antonjan/africube_receiver_board/gerber/msisdr-F_SilkS.pdf

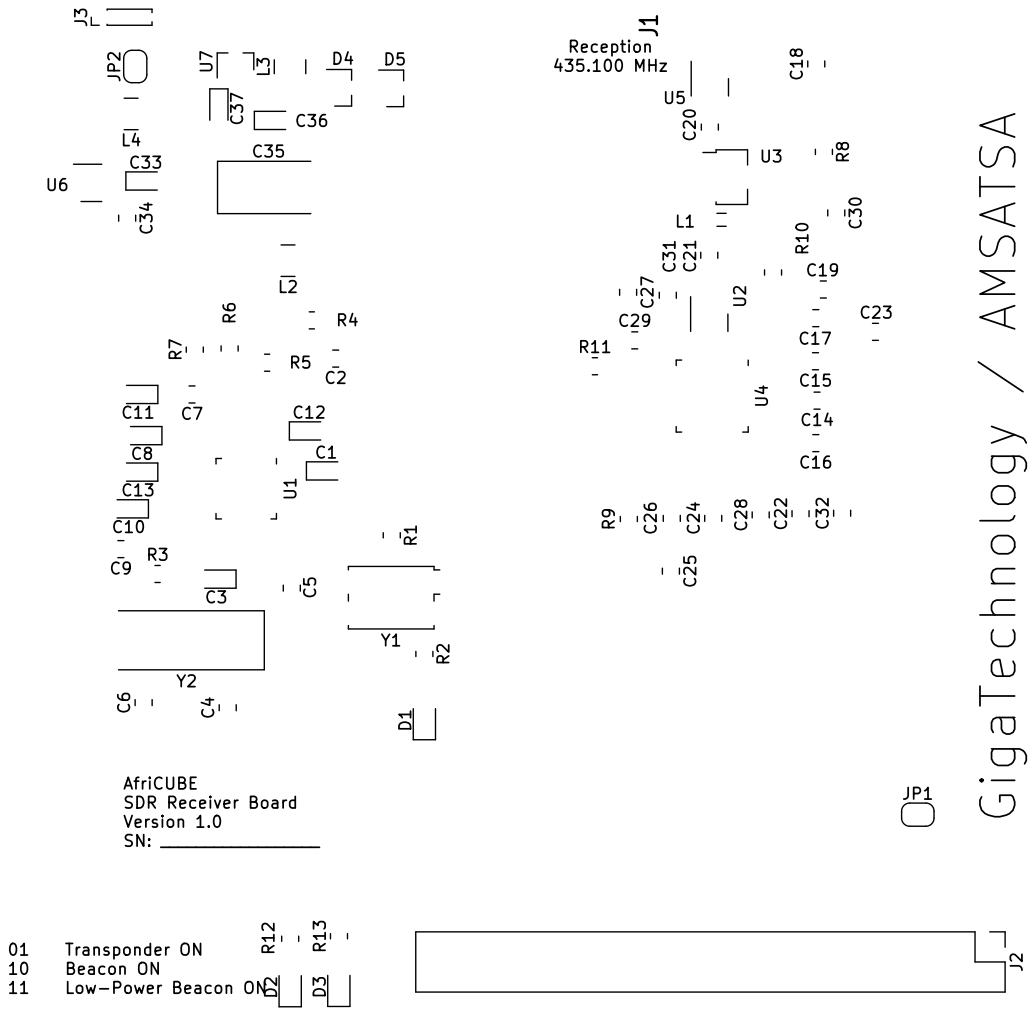
[picture p13: page 1]

01 Transponder ON
10 Beacon ON
11 Low-Power Beacon ON
