antonjan/africube_receiver_board/msiSDR-master/gerber/msisdr-F_SilkS.pdf

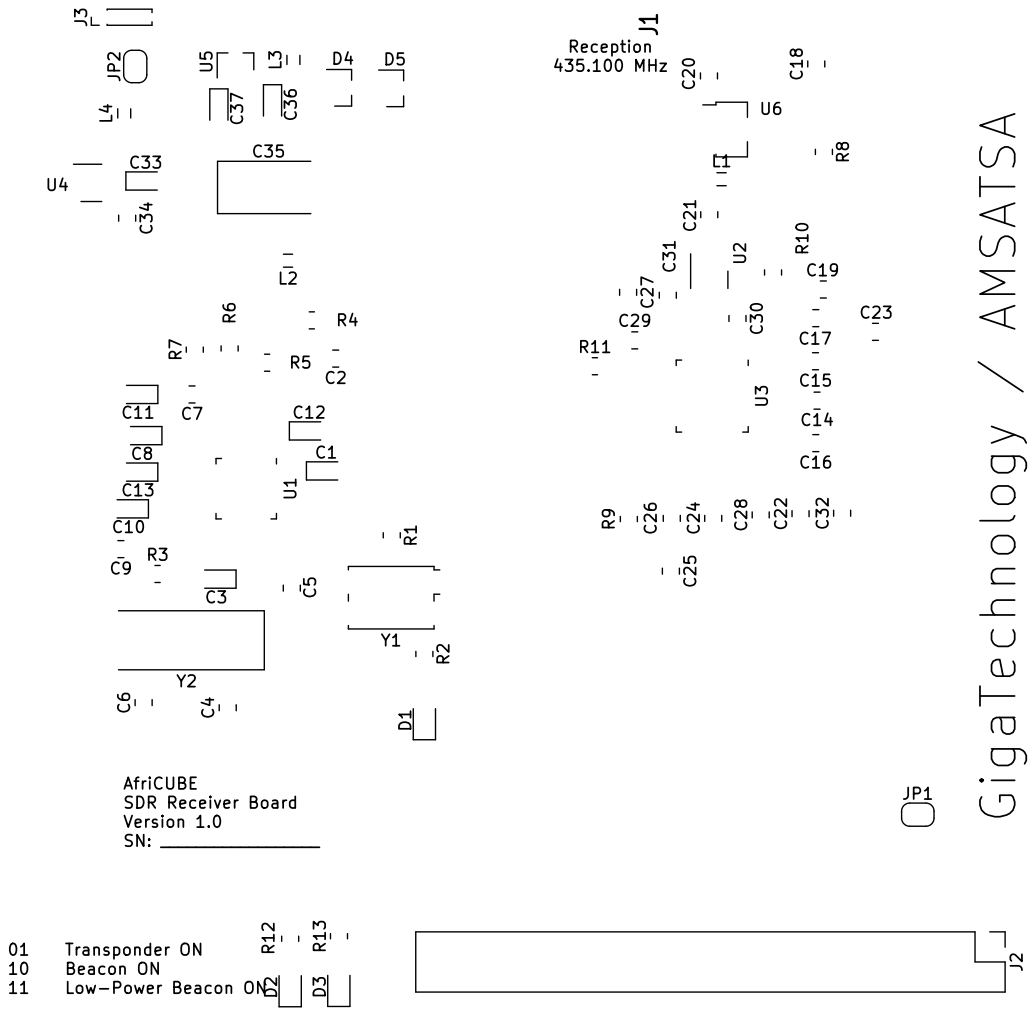
[picture p14: page 1]

01 Transponder ON
10 Beacon ON
11 Low-Power Beacon ON
