antonjan/africube_receiver_board/gerber/msisdr-Edge_Cuts.pdf

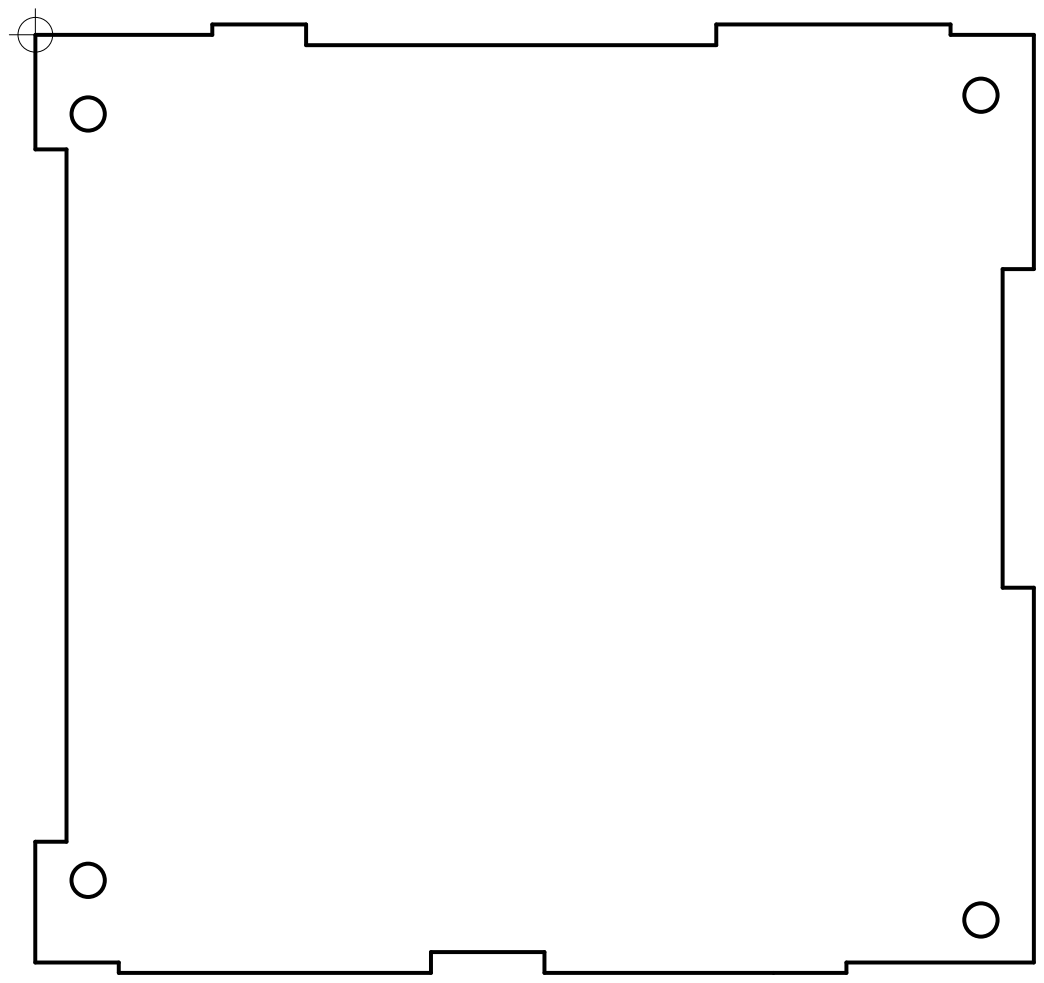
[picture p20: page 1]
