antonjan/africube_receiver_board/gerber/msisdr-F_Cu.pdf

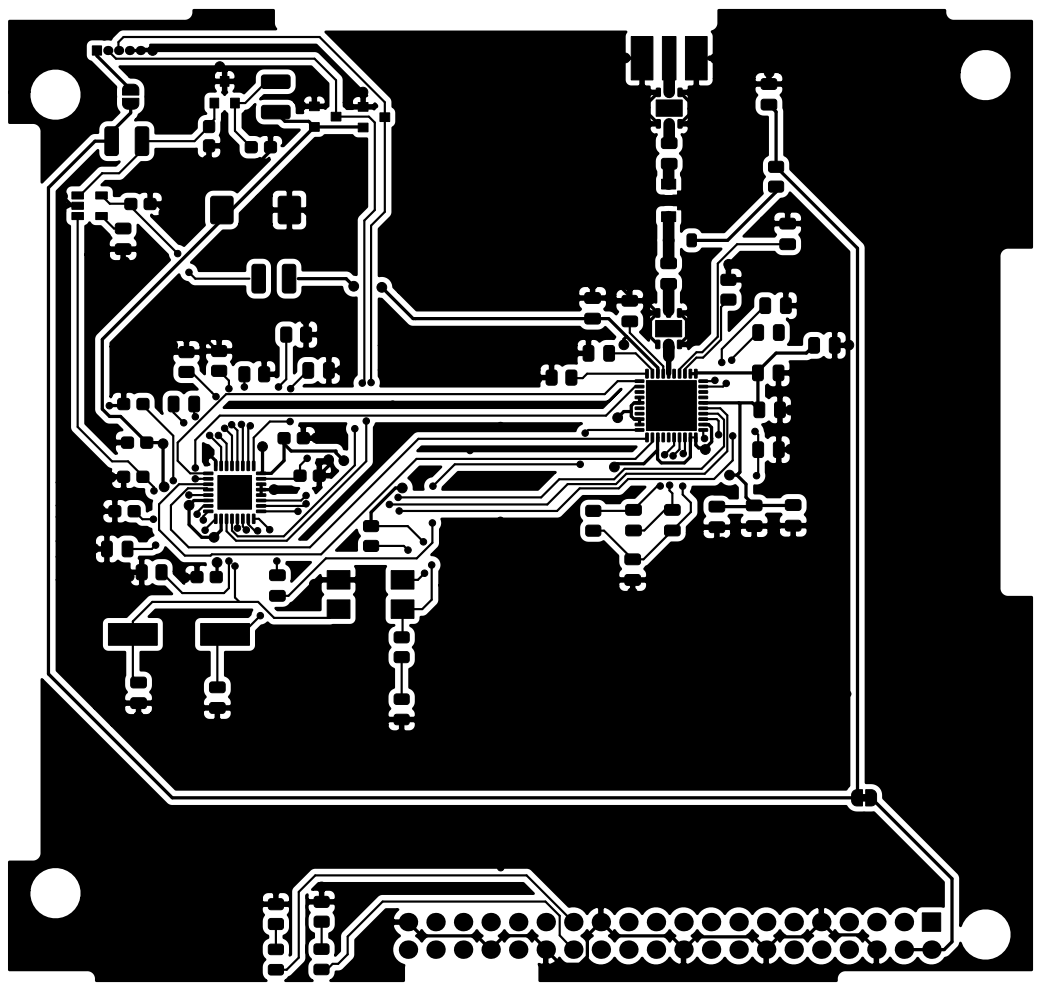
[picture p21: page 1]
