antonjan/africube_receiver_board/gerber/msisdr-F_Mask.pdf

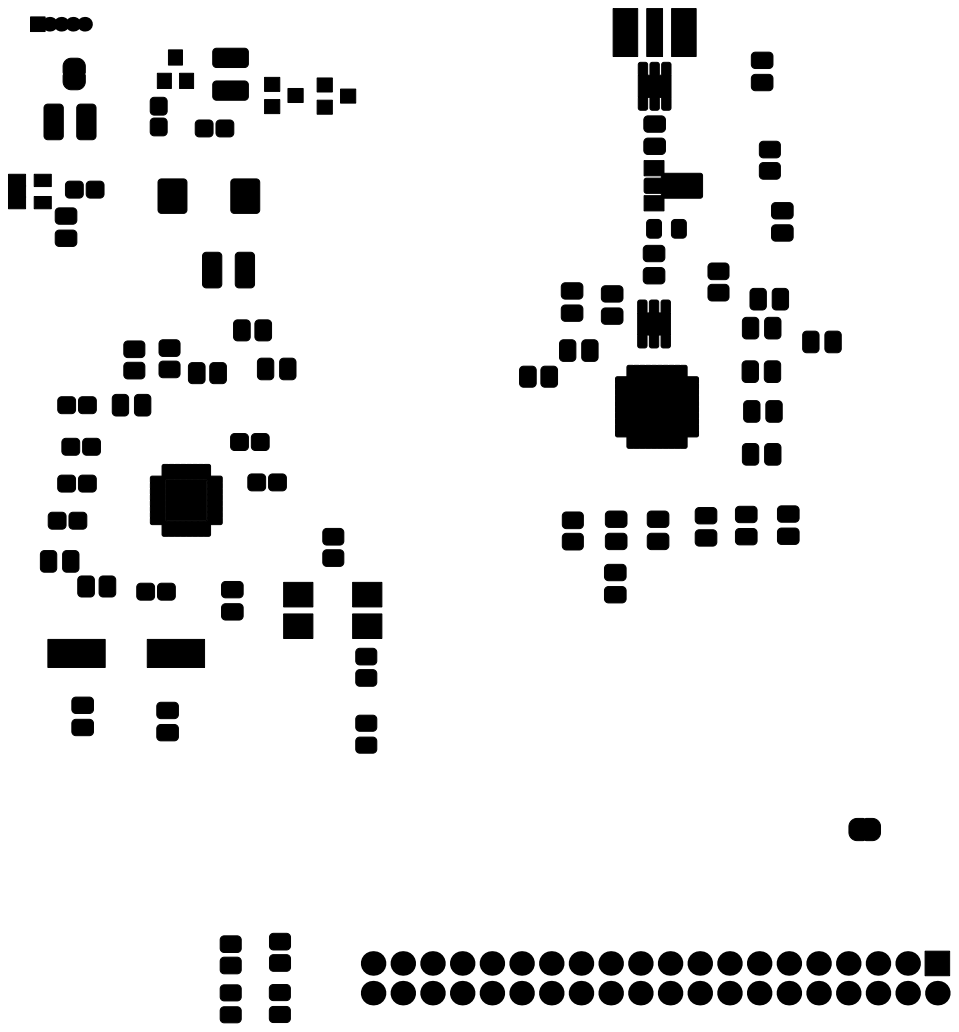
[picture p22: page 1]
