antonjan/africube_receiver_board/gerber/msisdr-F_Paste.pdf

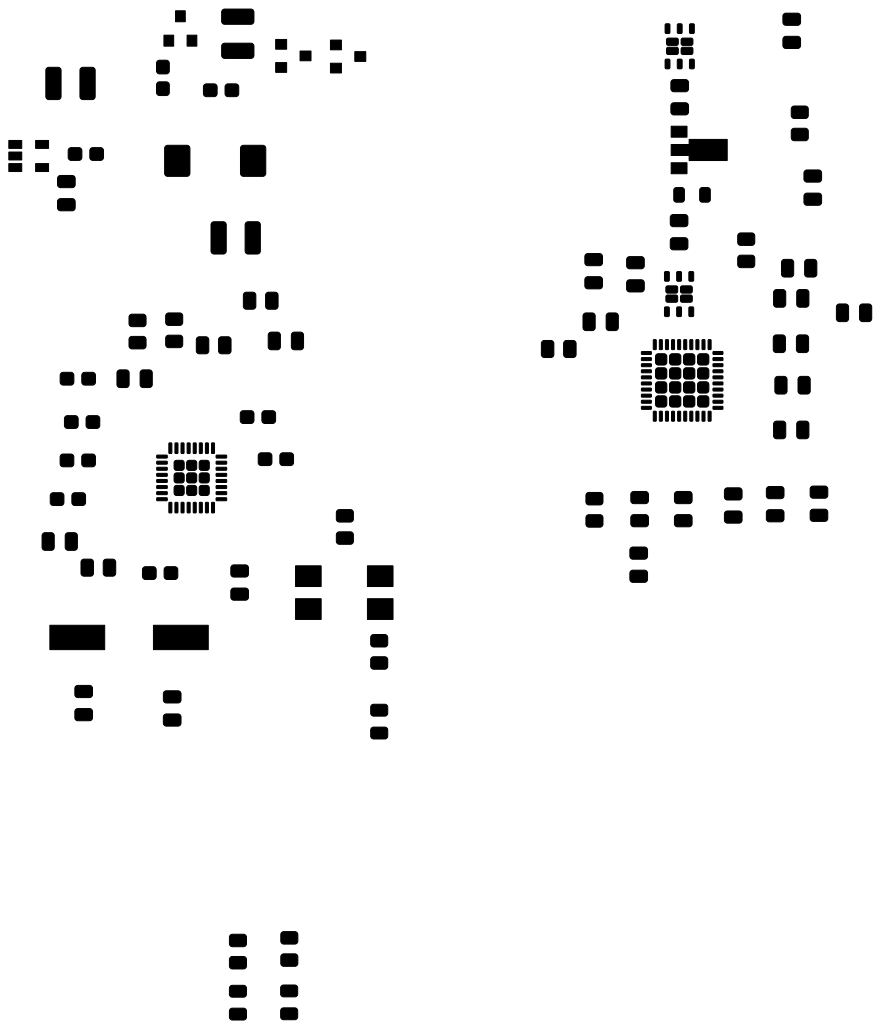
[picture p23: page 1]
