antonjan/africube_receiver_board/msiSDR-master/gerber/msisdr-B_Cu.pdf

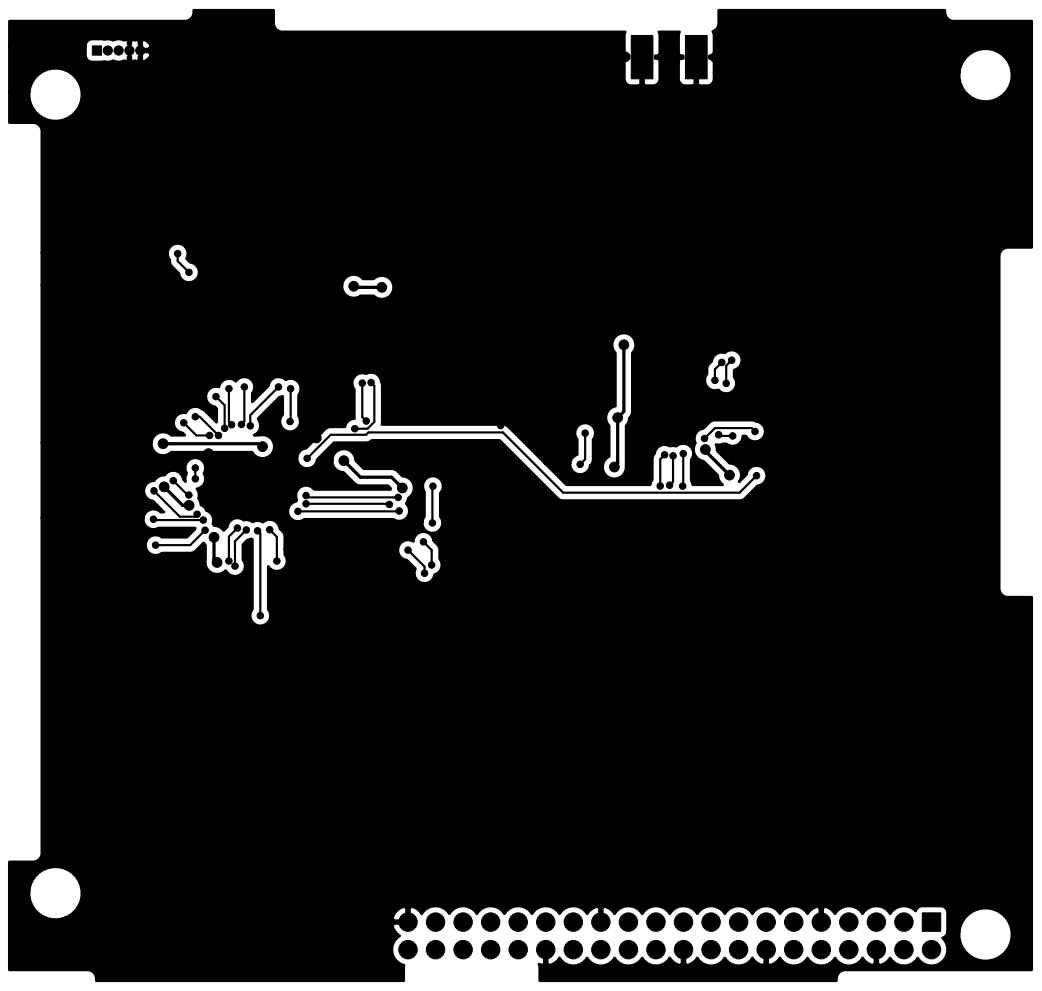
[picture p24: page 1]
