antonjan/africube_receiver_board/msiSDR-master/gerber/msisdr-B_Mask.pdf

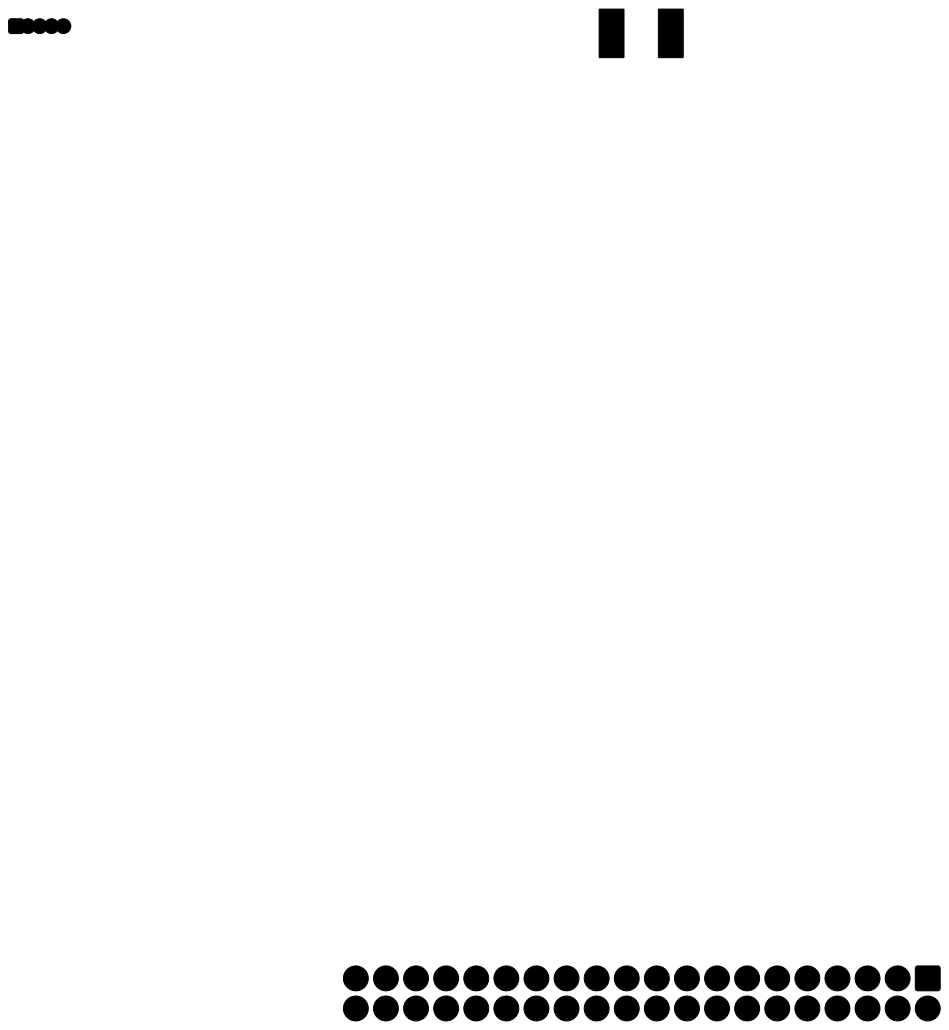
[picture p25: page 1]
