antonjan/africube_receiver_board/msiSDR-master/gerber/msisdr-F_Cu.pdf

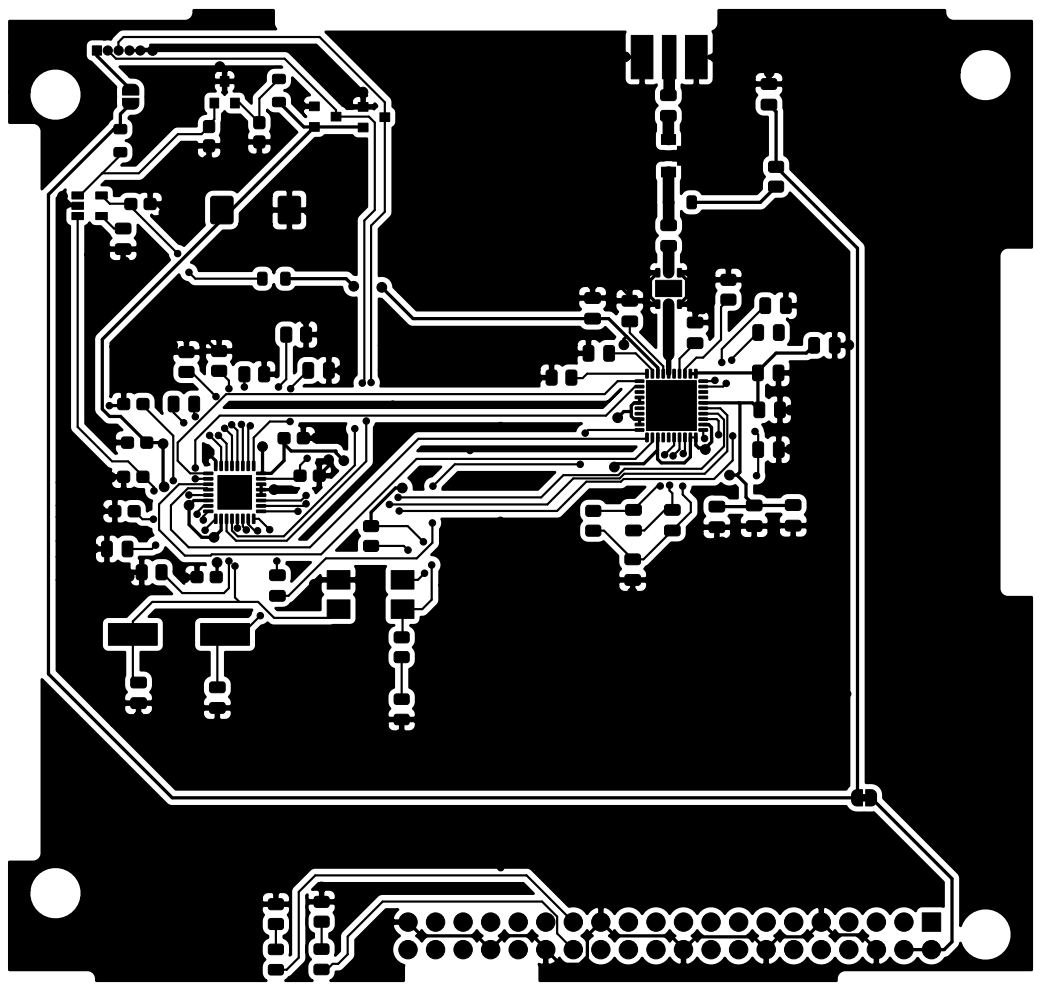
[picture p26: page 1]
