antonjan/africube_receiver_board/msiSDR-master/gerber/msisdr-F_Mask.pdf

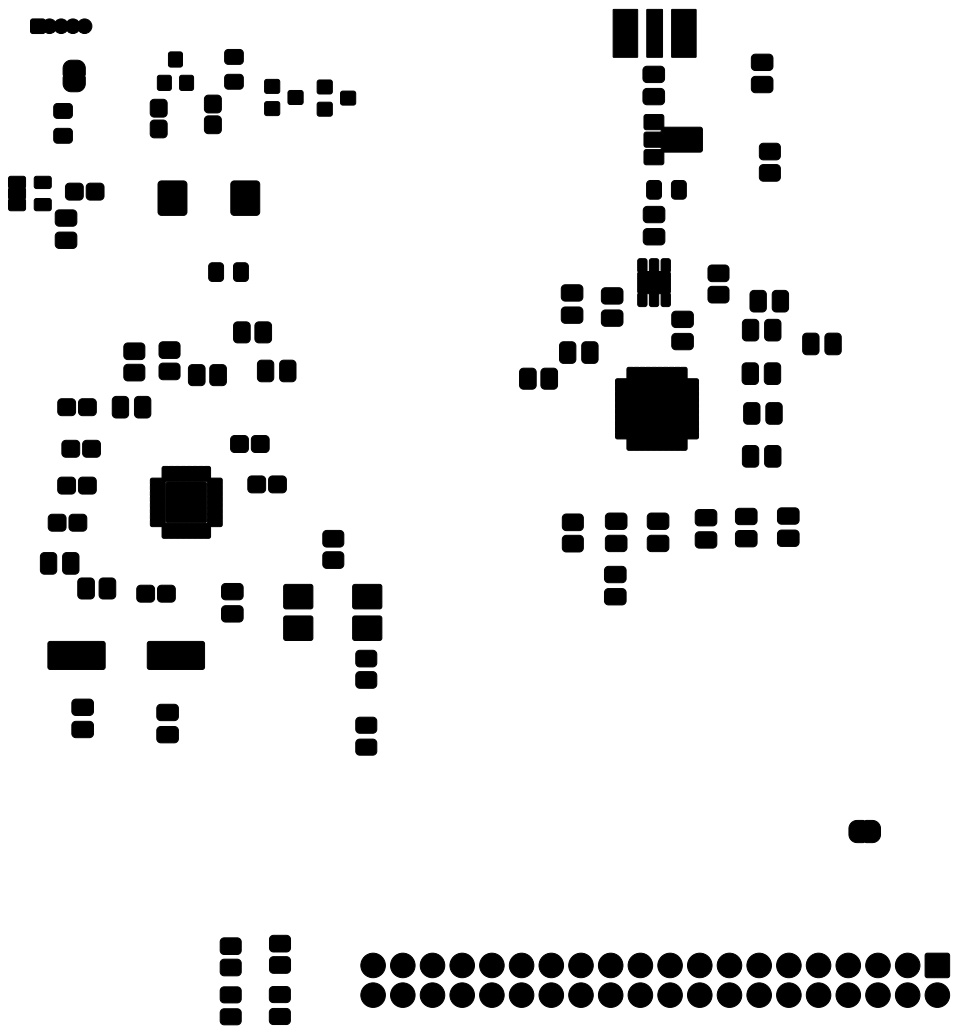
[picture p27: page 1]
