antonjan/africube_receiver_board/msiSDR-master/gerber/msisdr-F_Paste.pdf

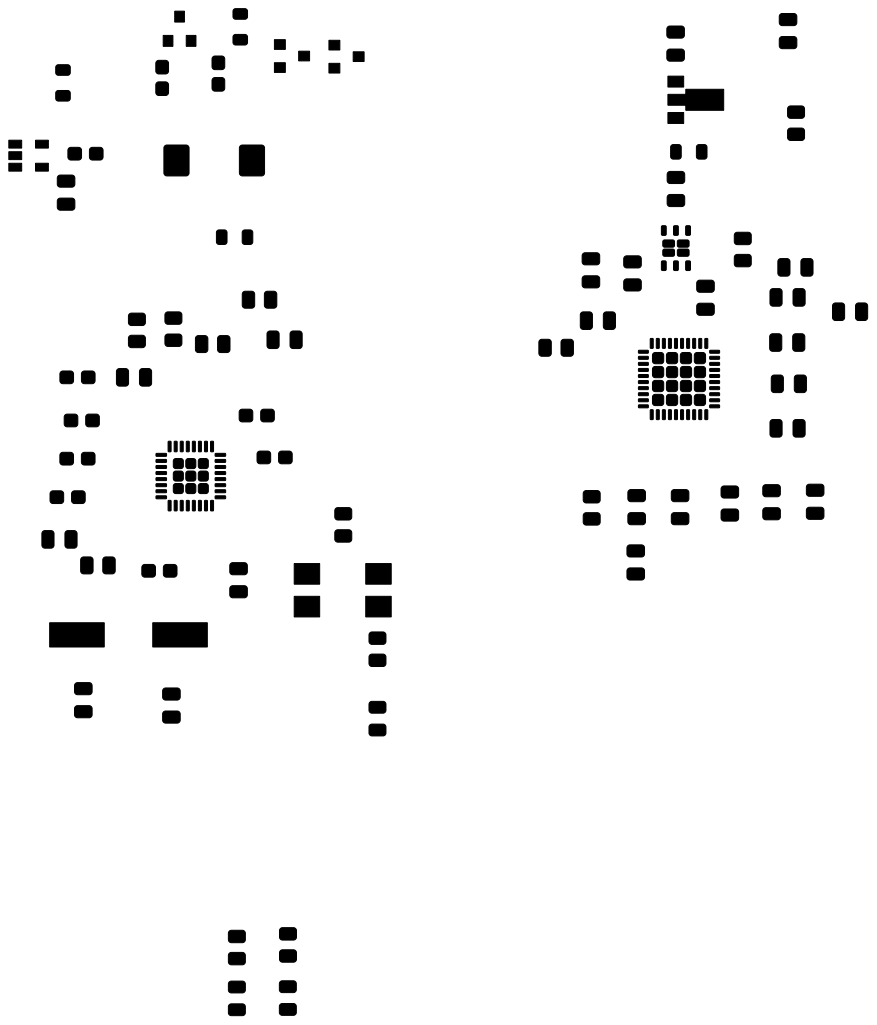
[picture p28: page 1]
